tillitis/tillitis-key1/hw/application_fpga/apps/defaultapp/main.c

// SPDX-FileCopyrightText: 2025 Tillitis AB <tillitis.se>
// SPDX-License-Identifier: BSD-2-Clause

#include <fw/tk1/reset.h>
#include <fw/tk1/syscall_num.h>
#include <syscall.h>
#include <tkey/debug.h>
#include <tkey/led.h>

int main(void)
{
	struct reset rst = {0};

	led_set(LED_BLUE);

	rst.type = START_CLIENT;
	syscall(TK1_SYSCALL_RESET, (uint32_t)&rst, 0, 0);
}
