tillitis/tillitis-key1/hw/application_fpga/core/tk1/rtl/tk1_spi_master.v

//======================================================================
//
// tk1_spi_master.v
// ----------------
// Minimal SPI master to be integrated into the tk1 module.
// The SPI master is able to generate a clock, and transfer,
// exchange a single byte with the slave.
//
// This master is compatible with the Winbond W25Q80DV memory.
// This means that MSB of a response from the memory is provided
// on the falling clock edge on the LSB of the command byte, not
// on a dummy byte. This means that the response spans the boundary
// of the bytes, The core handles this by sampling the MISO
// just prior to settint the positive clock flank at the start
// of a byte transfer.
//
//
// Author: Joachim Strombergson
// SPDX-FileCopyrightText: 2023 Tillitis AB <tillitis.se>
// SPDX-License-Identifier: BSD-2-Clause
//
//======================================================================

`default_nettype none

module tk1_spi_master (
    input wire clk,
    input wire reset_n,

    output wire spi_ss,
    output wire spi_sck,
    output wire spi_mosi,
    input  wire spi_miso,

    input  wire         spi_enable,
    input  wire         spi_enable_vld,
    input  wire         spi_start,
    input  wire [7 : 0] spi_tx_data,
    input  wire         spi_tx_data_vld,
    output wire [7 : 0] spi_rx_data,
    output wire         spi_ready
);


  //----------------------------------------------------------------
  // Internal constant and parameter definitions.
  //----------------------------------------------------------------
  localparam CTRL_IDLE = 3'h0;
  localparam CTRL_POS_FLANK = 3'h1;
  localparam CTRL_NEG_FLANK = 3'h2;
  localparam CTRL_NEXT = 3'h3;


  //----------------------------------------------------------------
  // Registers including update variables and write enable.
  //----------------------------------------------------------------
  reg         spi_ss_reg;

  reg         spi_csk_reg;
  reg         spi_csk_new;
  reg         spi_csk_we;

  reg [7 : 0] spi_tx_data_reg;
  reg [7 : 0] spi_tx_data_new;
  reg         spi_tx_data_nxt;
  reg         spi_tx_data_we;

  reg [7 : 0] spi_rx_data_reg;
  reg [7 : 0] spi_rx_data_new;
  reg         spi_rx_data_nxt;
  reg         spi_rx_data_we;

  reg         spi_miso_sample_reg;

  reg [2 : 0] spi_bit_ctr_reg;
  reg [2 : 0] spi_bit_ctr_new;
  reg         spi_bit_ctr_rst;
  reg         spi_bit_ctr_inc;
  reg         spi_bit_ctr_we;

  reg         spi_ready_reg;
  reg         spi_ready_new;
  reg         spi_ready_we;

  reg [2 : 0] spi_ctrl_reg;
  reg [2 : 0] spi_ctrl_new;
  reg         spi_ctrl_we;


  //----------------------------------------------------------------
  // Concurrent connectivity for ports etc.
  //----------------------------------------------------------------
  assign spi_ss      = spi_ss_reg;
  assign spi_sck     = spi_csk_reg;
  assign spi_mosi    = spi_tx_data_reg[7];
  assign spi_rx_data = spi_rx_data_reg;
  assign spi_ready   = spi_ready_reg;
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
